kercle/microscopy/hardware/cad/mounting/Reducer Lense - Clamp.step

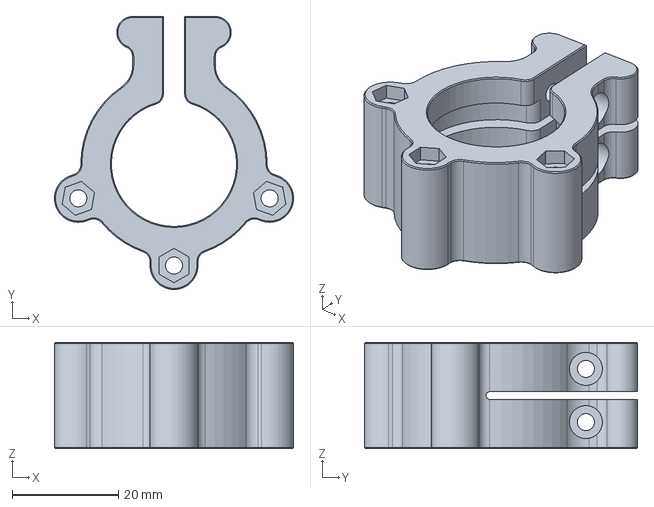
[picture p22: CAD file, 2025-11-01]
hardware/cad/mounting/Reducer Lense - Clamp.step
44.9 x 51.3 x 20.0 mm
