kercle/microscopy/hardware/controller-board/parts/models/YSPI1365.step

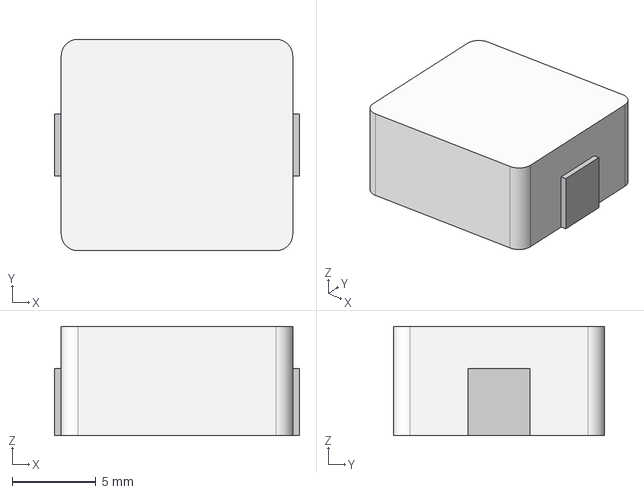
[picture p23: CAD file, 2025-09-05]
hardware/controller-board/parts/models/YSPI1365.step
14.6 x 12.6 x 6.50 mm
