kercle/microscopy/hardware/cad/mounting/Head Attachment - Bracket Top.step

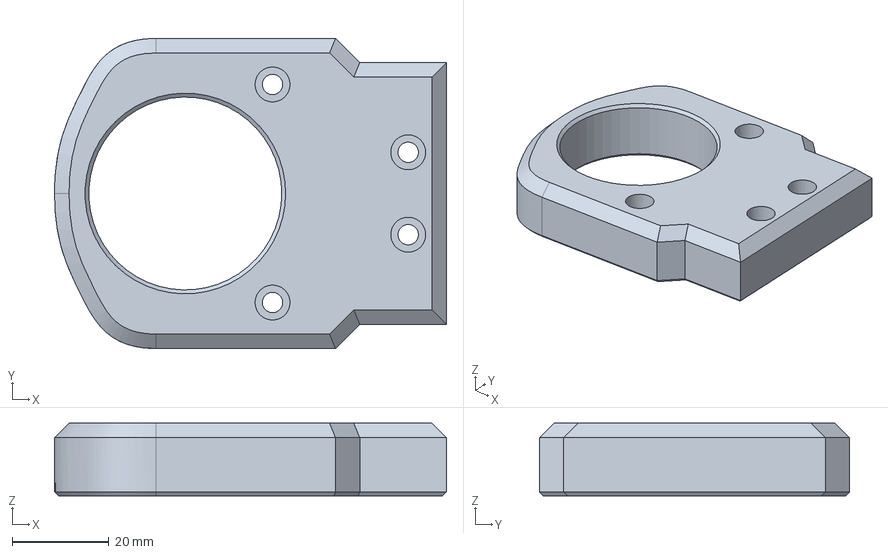
[picture p24: CAD file, 2025-11-01]
hardware/cad/mounting/Head Attachment - Bracket Top.step
80.9 x 64.0 x 15.0 mm
