kercle/microscopy/software/backend/src/data/test_image_a.jpg

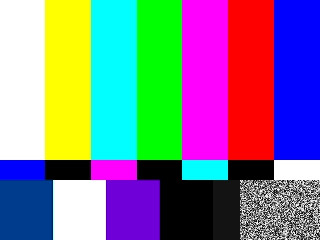
software/backend/src/data/test_image_a.jpg
